VOhmAster/ESP32-PWM-analyzer/Images/IMG_2.jpg

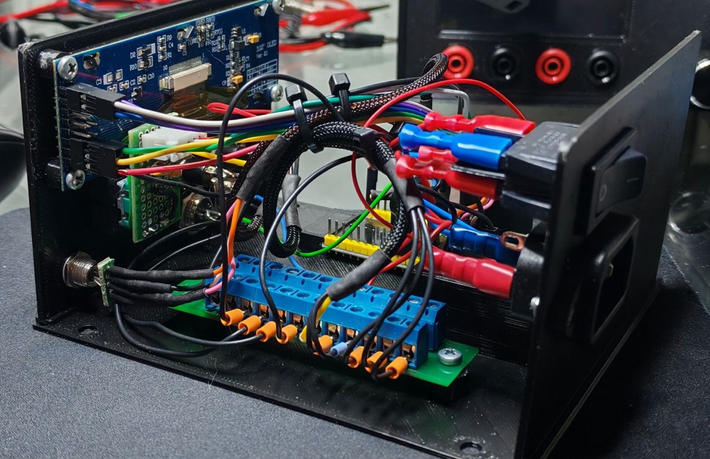
Images/IMG_2.jpg
