VOhmAster/ESP32-PWM-analyzer/Images/IMG_3.jpg

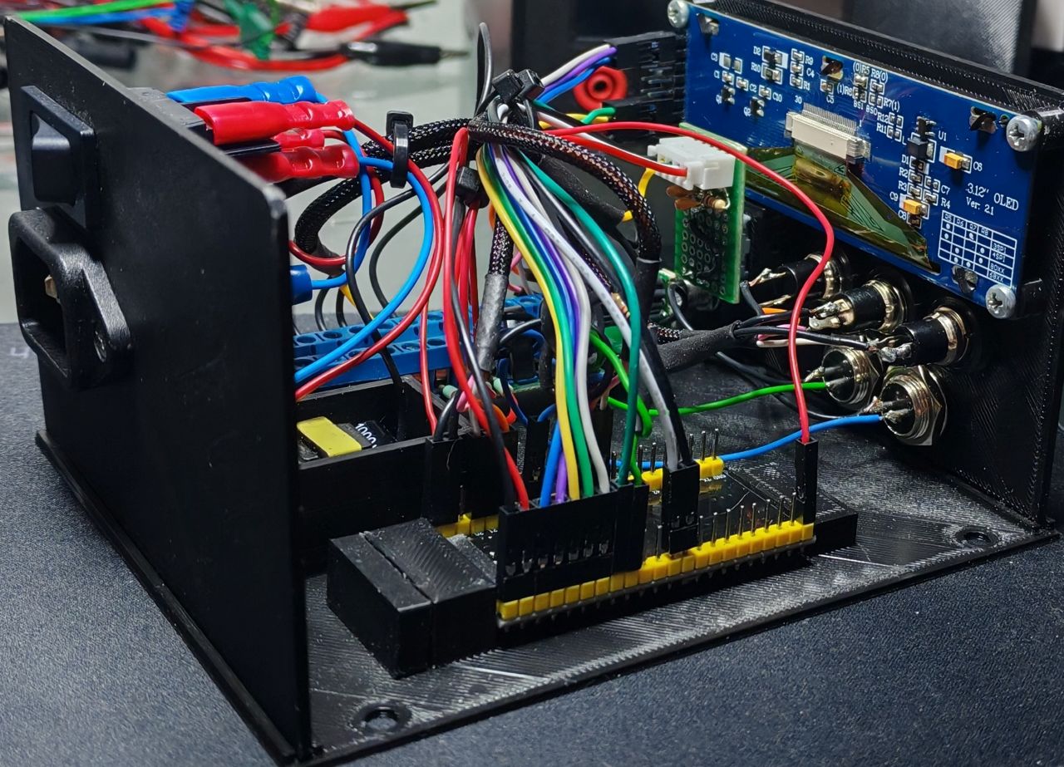
Images/IMG_3.jpg
