VOhmAster/ESP32-PWM-analyzer/Images/IMG_4.jpg

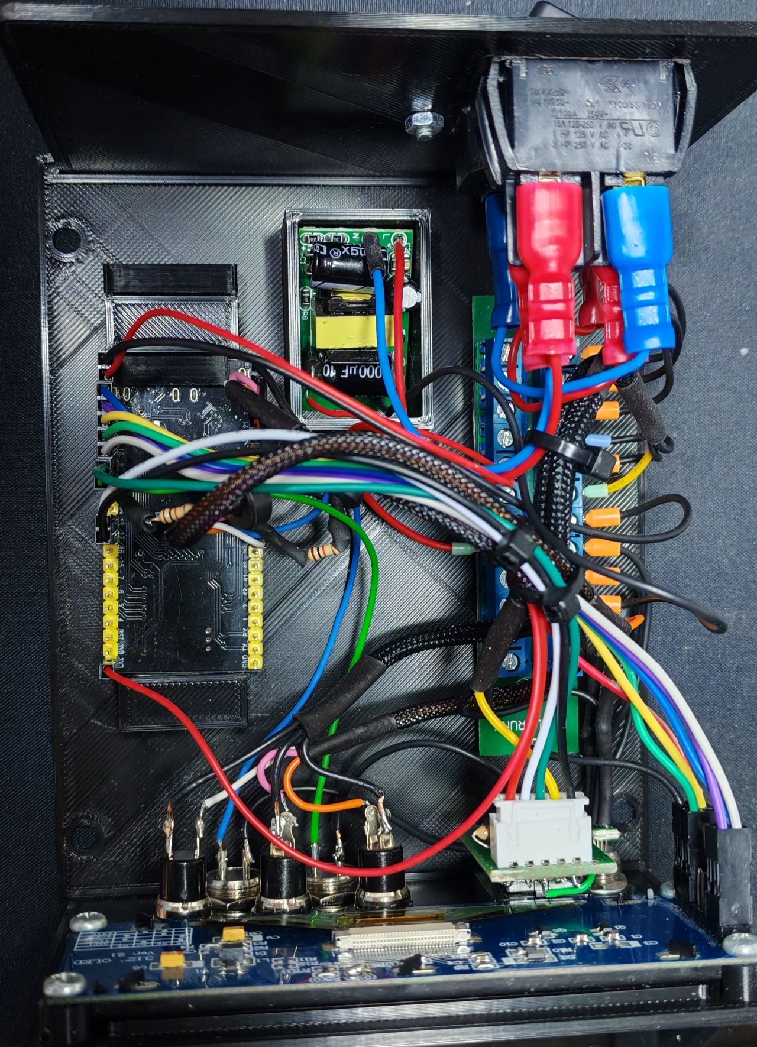
Images/IMG_4.jpg
