VOhmAster/ESP32-PWM-analyzer/Images/IMG_6.jpg

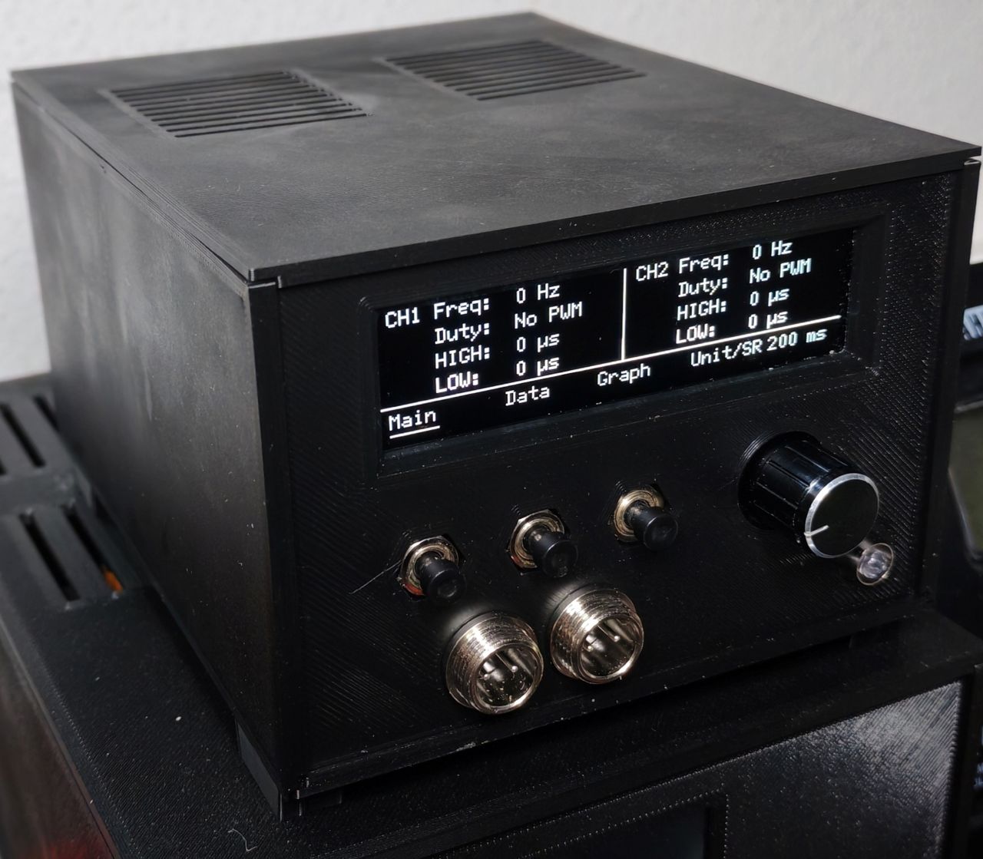
Images/IMG_6.jpg
